MovindiM/RGB-Colour-Sensor/PCB Final/Final Works/PCB BOTTOM LAYER VIEW.jpg

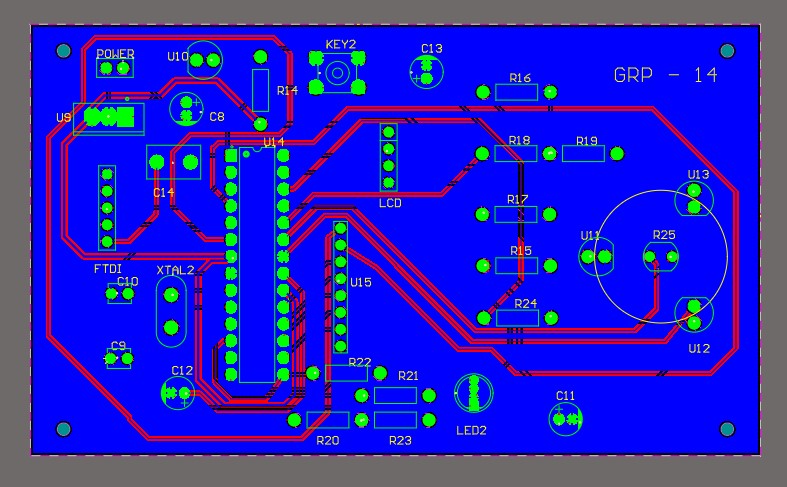
PCB Final/Final Works/PCB BOTTOM LAYER VIEW.jpg
