MovindiM/RGB-Colour-Sensor/PCB Final/Final Works/PCB SOLIDWORK EASYEDA VIEW.jpg

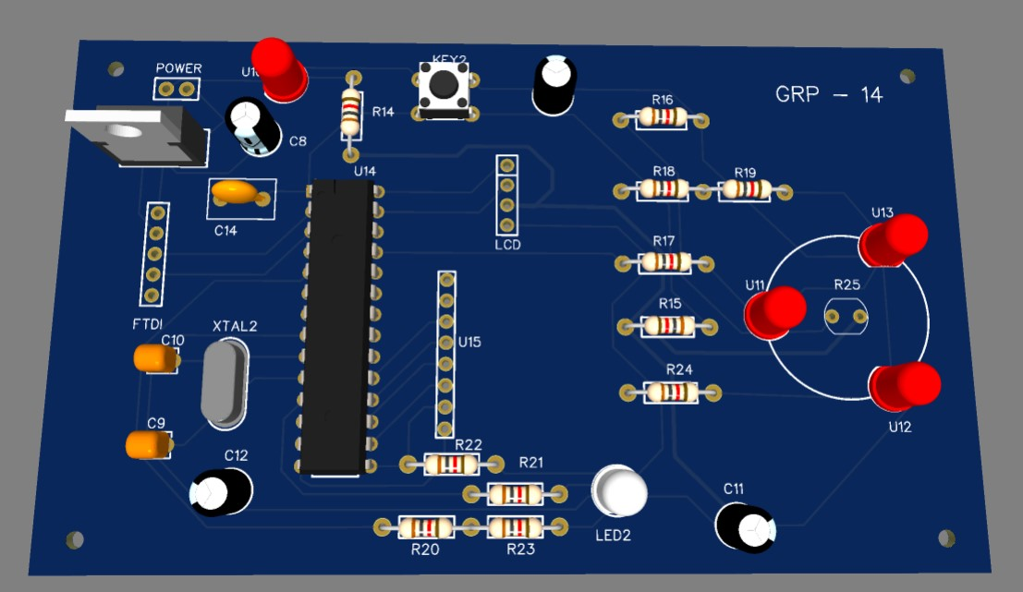
PCB Final/Final Works/PCB SOLIDWORK EASYEDA VIEW.jpg
