MovindiM/RGB-Colour-Sensor/PCB Final/Final Works/PCB SOLIDWORK TOP VIEW.jpg

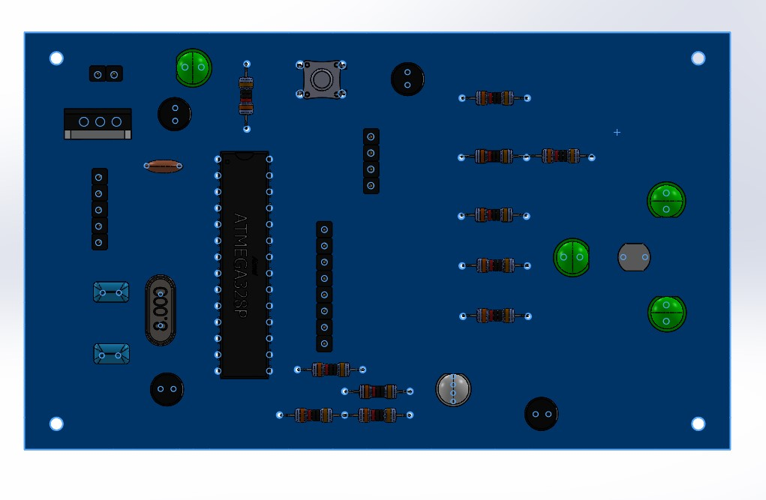
PCB Final/Final Works/PCB SOLIDWORK TOP VIEW.jpg
