MovindiM/RGB-Colour-Sensor/PCB Final/Final Works/PCB TOP LAYER VIEW.jpg

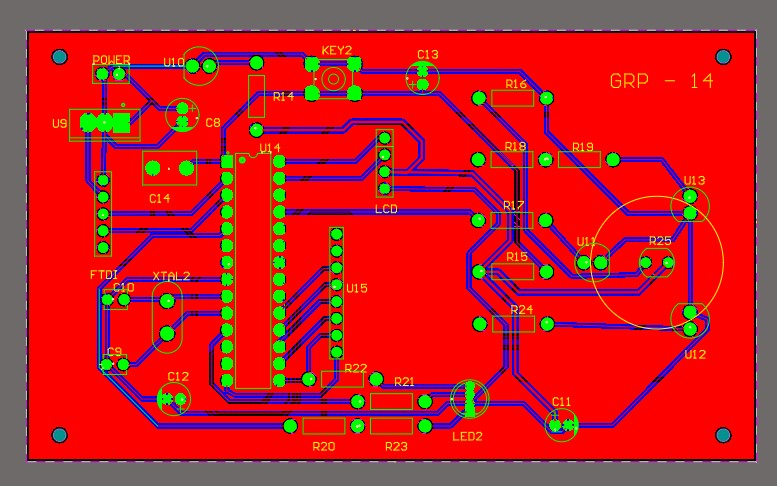
PCB Final/Final Works/PCB TOP LAYER VIEW.jpg
