MovindiM/RGB-Colour-Sensor/PCB Final/Final Works/SOLIDWORK ANGLE VIEW.jpg

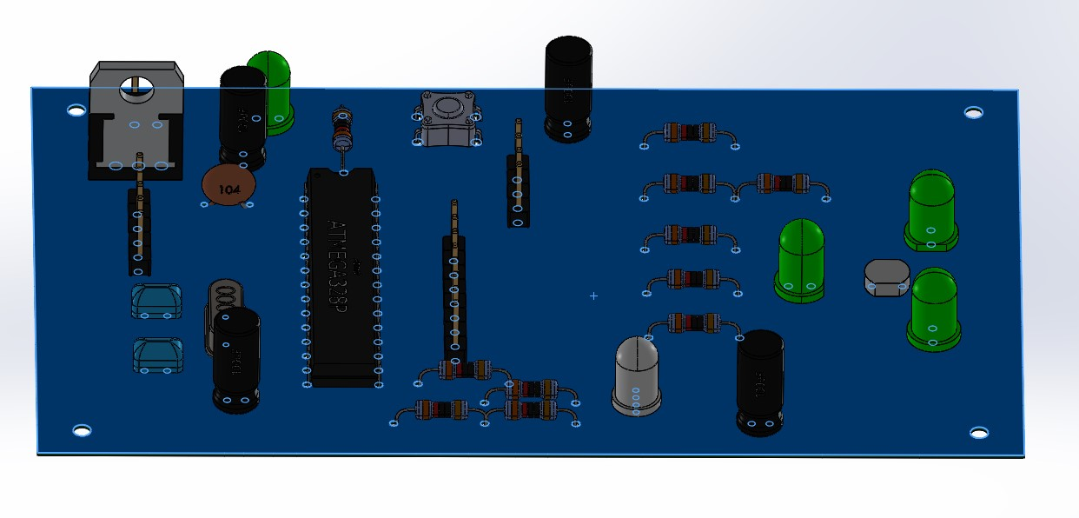
PCB Final/Final Works/SOLIDWORK ANGLE VIEW.jpg
