MovindiM/RGB-Colour-Sensor/PCB Final/PCB 3D Back View.jpg

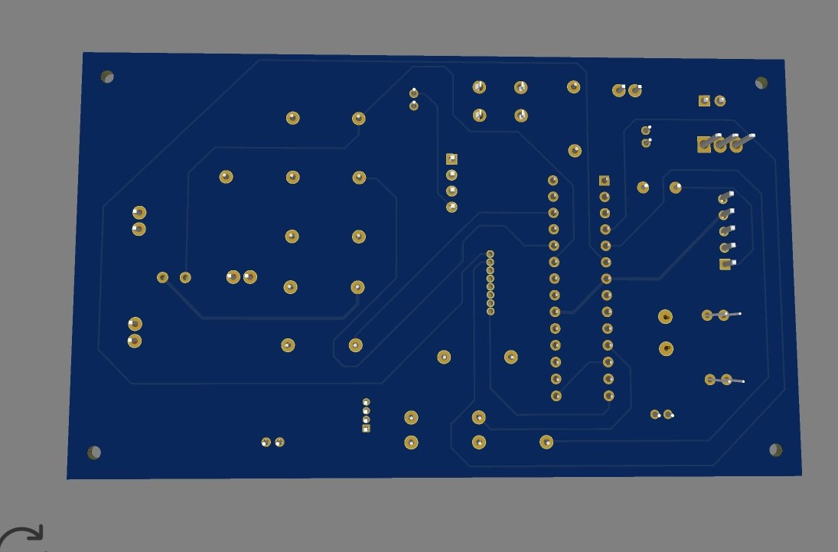
PCB Final/PCB 3D Back View.jpg
