MovindiM/RGB-Colour-Sensor/PCB Final/PCB 3D Front View.jpg

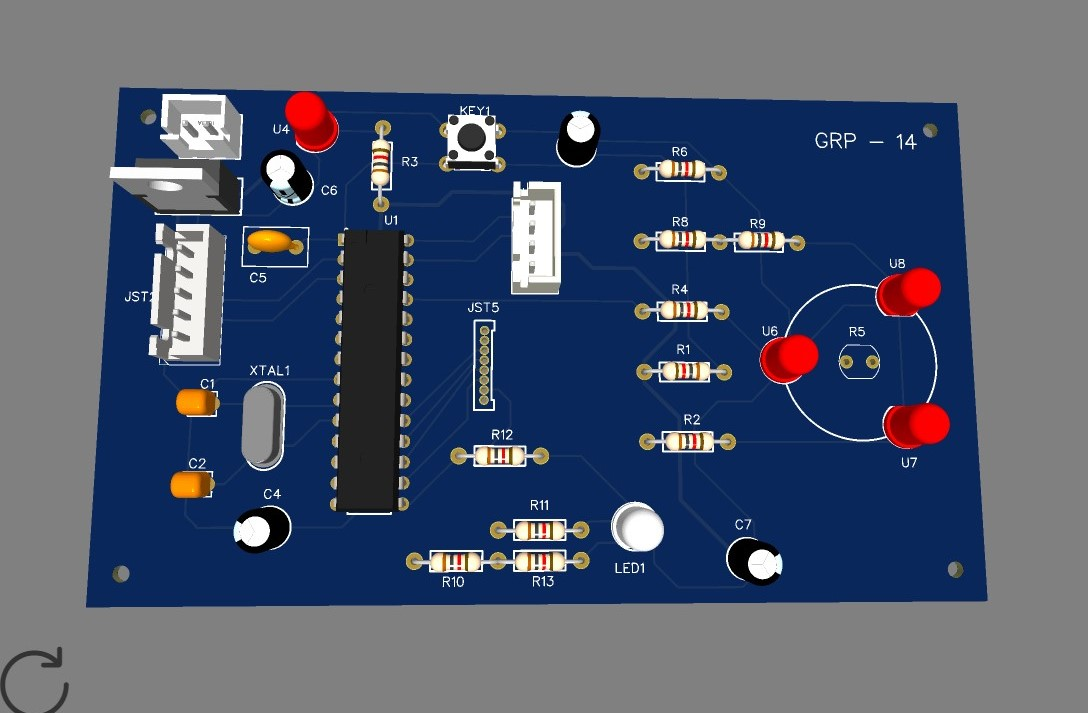
PCB Final/PCB 3D Front View.jpg
