MovindiM/RGB-Colour-Sensor/Physical_Arduino_Device/Output_colors/Blue_output.png

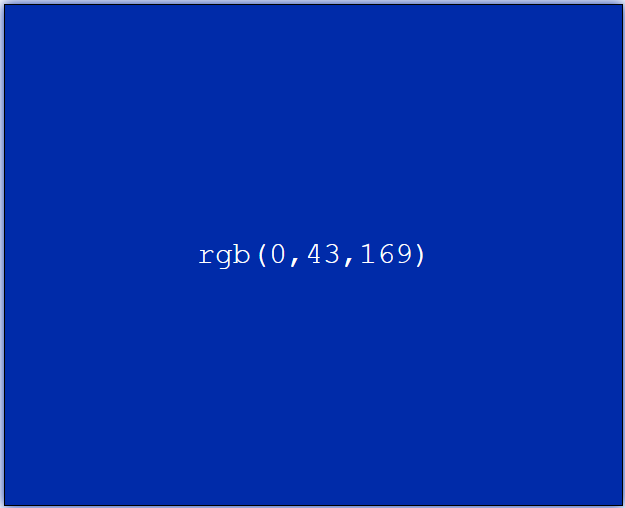
Physical_Arduino_Device/Output_colors/Blue_output.png
