MovindiM/RGB-Colour-Sensor/Physical_Arduino_Device/Output_colors/Green_output.png

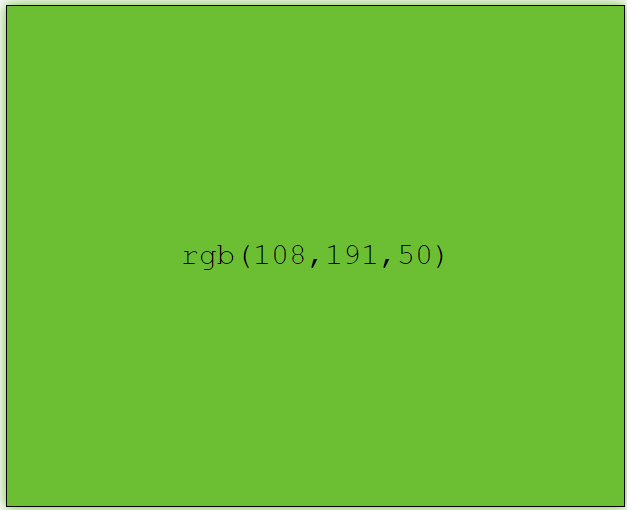
Physical_Arduino_Device/Output_colors/Green_output.png
