MovindiM/RGB-Colour-Sensor/Physical_Arduino_Device/Output_colors/White_output.png

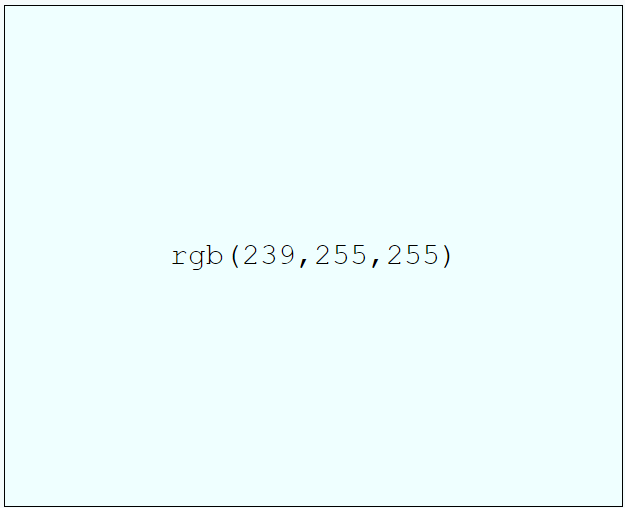
Physical_Arduino_Device/Output_colors/White_output.png
