MovindiM/RGB-Colour-Sensor/Physical_Arduino_Device/photos/Color_cards.jpg

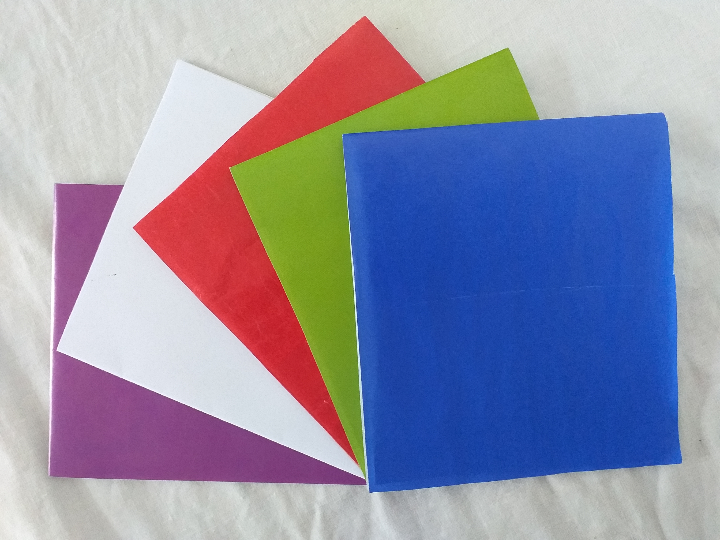
Physical_Arduino_Device/photos/Color_cards.jpg
