MovindiM/RGB-Colour-Sensor/Physical_Arduino_Device/photos/Violet.jpg

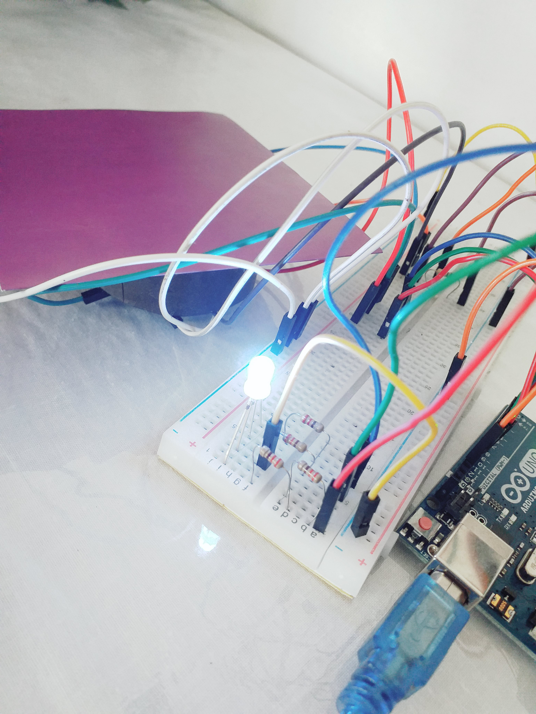
Physical_Arduino_Device/photos/Violet.jpg
