MovindiM/RGB-Colour-Sensor/enclosure/smt_resistor101.sldprt

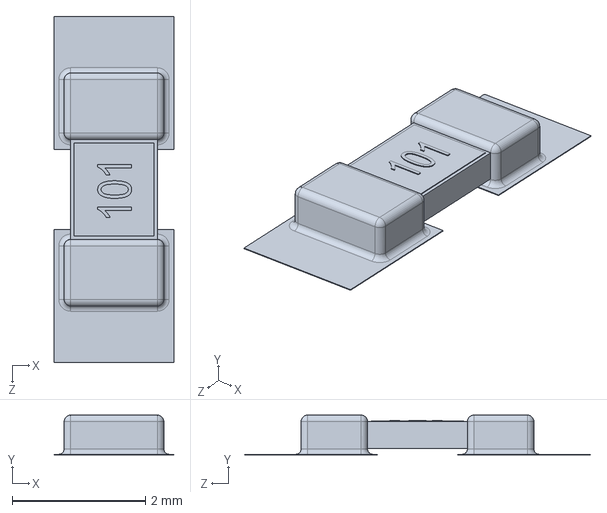
[picture p50: CAD file, 2021-08-11]
enclosure/smt_resistor101.sldprt
1.80 x 0.6 x 5.20 mm
