MovindiM/RGB-Colour-Sensor/enclosure/backlight.SLDPRT

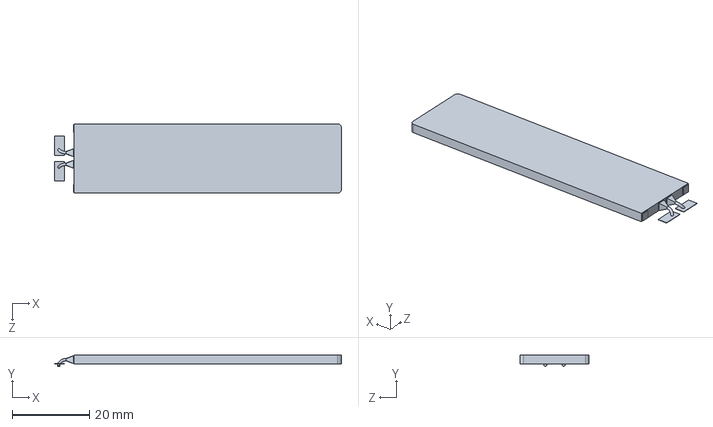
[picture p51: CAD file, 2021-08-11]
enclosure/backlight.SLDPRT
74.4 x 2.98 x 18.0 mm
