MovindiM/RGB-Colour-Sensor/enclosure/pcb.SLDPRT

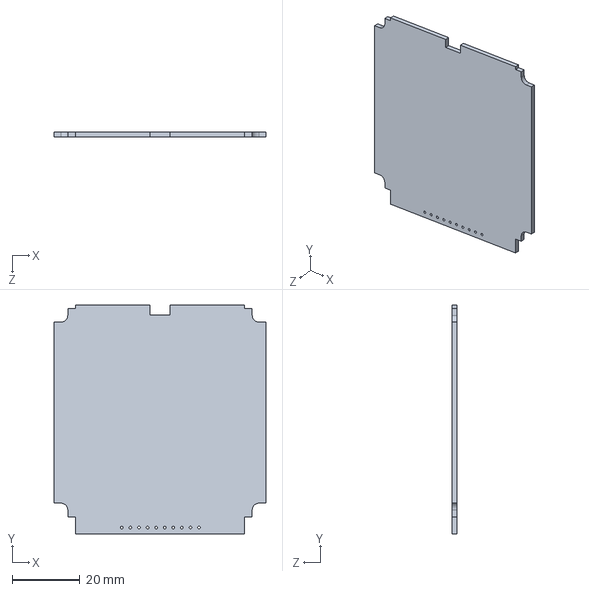
[picture p52: CAD file, 2021-08-11]
enclosure/pcb.SLDPRT
62.7 x 67.8 x 1.55 mm
