MovindiM/RGB-Colour-Sensor/enclosure/16pin_header__.sldprt

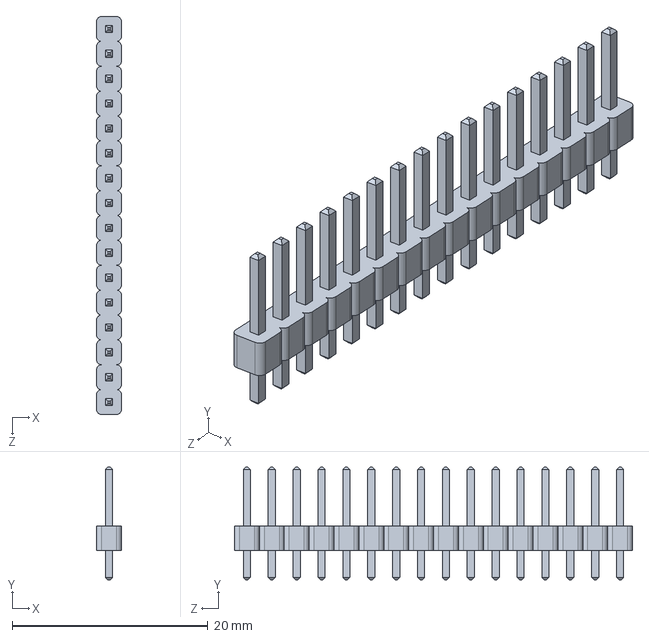
[picture p53: CAD file, 2021-08-11]
enclosure/16pin_header__.sldprt
2.54 x 11.5 x 40.6 mm
