MovindiM/RGB-Colour-Sensor/enclosure/enclosure.SLDPRT

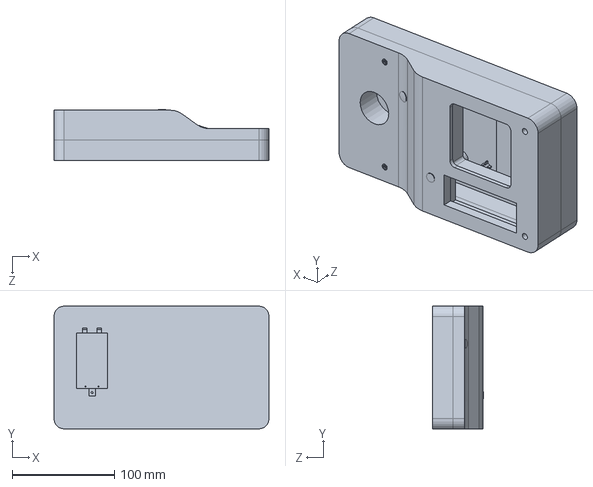
[picture p54: CAD file, 2021-08-11]
enclosure/enclosure.SLDPRT
210.0 x 120.0 x 49.5 mm
